dzh121/All-In-One-Clock-2.0/code/icons.h

#include <avr/pgmspace.h>

const uint16_t alarmIcon[0x1000] PROGMEM ={
0x0000, 0x0000, 0x0000, 0x0000, 0x0000, 0x0000, 0x0000, 0x0000, 0x0000, 0x0000, 0x10A2, 0x3186, 0x4228, 0x39E7, 0x2124, 0x0841,   // 0x0010 (16) pixels
0x0000, 0x0000, 0x0000, 0x0000, 0x0000, 0x0000, 0x0000, 0x0000, 0x0000, 0x0000, 0x0000, 0x0000, 0x0000, 0x4A49, 0xB596, 0xE71C,   // 0x0020 (32) pixels
0xE71C, 0xB5B6, 0x52AA, 0x0020, 0x0000, 0x0000, 0x0000, 0x0000, 0x0000, 0x0000, 0x0000, 0x0000, 0x0000, 0x0000, 0x0000, 0x0000,   // 0x0030 (48) pixels
0x0020, 0x2124, 0x39C7, 0x39C7, 0x2965, 0x10A2, 0x0000, 0x0000, 0x0000, 0x0000, 0x0000, 0x0000, 0x0000, 0x0000, 0x0000, 0x0000,   // 0x0040 (64) pixels
0x0000, 0x0000, 0x0000, 0x0000, 0x0000, 0x0000, 0x0000, 0x0020, 0x31A6, 0x8C51, 0xCE59, 0xE73C, 0xF79E, 0xF79E, 0xDEFB, 0xB5B6,   // 0x0050 (80) pixels
0x632C, 0x10A2, 0x0000, 0x0000, 0x0000, 0x0000, 0x0000, 0x0000, 0x0000, 0x0000, 0x0000, 0x0000, 0x6B6D, 0xEF5D, 0xFFFF, 0xFFFF,   // 0x0060 (96) pixels
0xFFFF, 0xFFFF, 0xF79E, 0x7BCF, 0x0020, 0x0000, 0x0000, 0x0000, 0x0000, 0x0000, 0x0000, 0x0000, 0x0000, 0x0000, 0x0861, 0x52AA,   // 0x0070 (112) pixels
0xAD75, 0xDEFB, 0xEF7D, 0xEF7D, 0xE73C, 0xCE59, 0x8C71, 0x39E7, 0x0020, 0x0000, 0x0000, 0x0000, 0x0000, 0x0000, 0x0000, 0x0000,   // 0x0080 (128) pixels
0x0000, 0x0000, 0x0000, 0x0000, 0x0000, 0x0000, 0x2104, 0x94B2, 0xEF5D, 0xFFFF, 0xFFFF, 0xFFFF, 0xFFFF, 0xFFFF, 0xFFFF, 0xFFFF,   // 0x0090 (144) pixels
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
	0x1861, 0x5945, 0x5945, 0x5945, 0x5945, 0x5945, 0x5945, 0x5145, 0x0000, 0x2882, 0x5945, 0x5945, 0x5945, 0x5945, 0x5945, 0x5945, 
	0x4924, 0x0000, 0x30c3, 0x5945, 0x5945, 0x5945, 0x5945, 0x5945, 0x5945, 0x5945, 0x4924, 0x1041, 0x0000, 0x0000, 0x0000, 0x0000, 
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
};
